stone-voices/vasvas/hardware/vasvas.kicad_sch

## KiCad design hardware/vasvas.kicad_sch (2025-12-18, an earlier design)

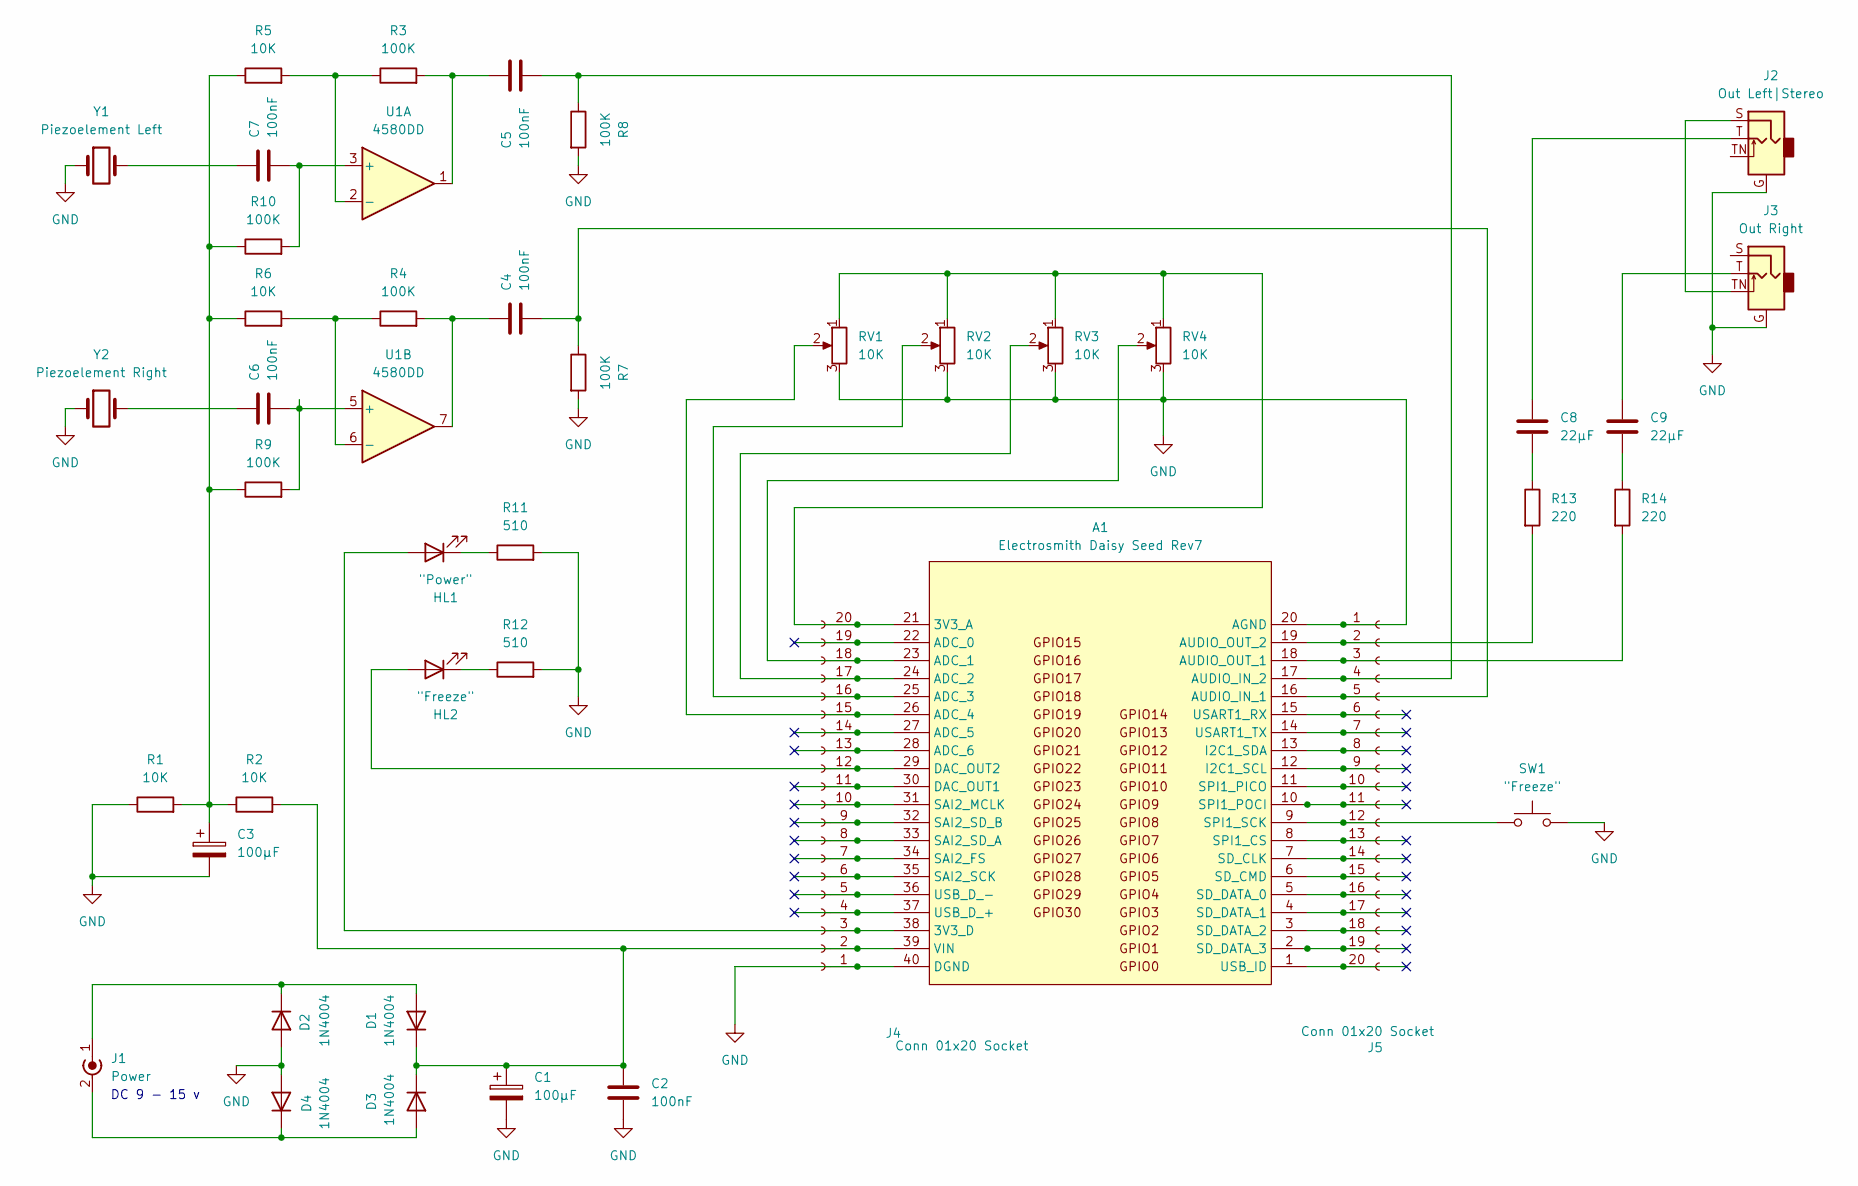
[picture p4: schematic vasvas.kicad_sch]

Parts:
A1: Electrosmith Daisy Seed Rev7
C1, C3: 100µF
C2, C4, C5, C6, C7: 100nF; C_0805_2012Metric
C8, C9: 22µF; C_0805_2012Metric
D1, D2, D3, D4: 1N4004; D_DO-41_SOD81_P10.16mm_Horizontal
HL1: "Power"
HL2: "Freeze"
J1: Power
J2: Out Left|Stereo
J3: Out Right
J4, J5: Conn 01x20 Socket; PinSocket1x20_P2.54mm_Vertical_JLCPCB
R1, R2, R5, R6: 10K; R_0805_2012Metric
R3, R4, R7, R8, R9, R10: 100K; R_0805_2012Metric
R11, R12: 510; R_0805_2012Metric
R13, R14: 220; R_0805_2012Metric
RV1, RV2, RV3, RV4: 10K
SW1: "Freeze"
U1: 4580DD
Y1: Piezoelement Left
Y2: Piezoelement Right

Connections:
GND: A1.20 (AGND), A1.40 (DGND), C1.2, C2.2, C3.2, D2.2 (A), D4.2 (A), J2.G, J3.G, J4.1, J5.1, R1.1, R7.2, R8.2, R11.2, R12.2, RV1.3, RV2.3, RV3.3, RV4.3, SW1.3 (B), SW1.4 (B), Y1.1, Y2.1
unnamed: A1.1 (USB_ID), J5.20
unnamed: A1.2 (SD_DATA_3), J5.19
unnamed: A1.3 (SD_DATA_2), J5.18
unnamed: A1.4 (SD_DATA_1), J5.17
unnamed: A1.5 (SD_DATA_0), J5.16
unnamed: A1.6 (SD_CMD), J5.15
unnamed: A1.7 (SD_CLK), J5.14
unnamed: A1.8 (SPI1_CS), J5.13
unnamed: A1.9 (SPI1_SCK), J5.12, SW1.1 (A), SW1.2 (A)
unnamed: A1.10 (SPI1_POCI), J5.11
unnamed: A1.11 (SPI1_PICO), J5.10
unnamed: A1.12 (I2C1_SCL), J5.9
unnamed: A1.13 (I2C1_SDA), J5.8
unnamed: A1.14 (USART1_TX), J5.7
unnamed: A1.15 (USART1_RX), J5.6
unnamed: A1.16 (AUDIO_IN_1), C4.2, J5.5, R7.1
unnamed: A1.17 (AUDIO_IN_2), C5.2, J5.4, R8.1
unnamed: A1.18 (AUDIO_OUT_1), J5.3, R14.2
unnamed: A1.19 (AUDIO_OUT_2), J5.2, R13.2
unnamed: A1.21 (3V3_A), J4.20, RV1.1, RV2.1, RV3.1, RV4.1
unnamed: A1.22 (ADC_0), J4.19
unnamed: A1.23 (ADC_1), J4.18, RV4.2
unnamed: A1.24 (ADC_2), J4.17, RV3.2
unnamed: A1.25 (ADC_3), J4.16, RV2.2
unnamed: A1.26 (ADC_4), J4.15, RV1.2
unnamed: A1.27 (ADC_5), J4.14
unnamed: A1.28 (ADC_6), J4.13
unnamed: A1.29 (DAC_OUT2), HL2.2 (A), J4.12
unnamed: A1.30 (DAC_OUT1), J4.11
unnamed: A1.31 (SAI2_MCLK), J4.10
unnamed: A1.32 (SAI2_SD_B), J4.9
unnamed: A1.33 (SAI2_SD_A), J4.8
unnamed: A1.34 (SAI2_FS), J4.7
unnamed: A1.35 (SAI2_SCK), J4.6
unnamed: A1.36 (USB_D_-), J4.5
unnamed: A1.37 (USB_D_+), J4.4
unnamed: A1.38 (3V3_D), HL1.2 (A), J4.3
unnamed: A1.39 (VIN), C1.1, C2.1, D1.1 (K), D3.1 (K), J4.2, R2.2
unnamed: C3.1, R1.2, R2.1, R5.1, R6.1, R9.1, R10.1
unnamed: C4.1, R4.2, U1.7
unnamed: C5.1, R3.2, U1.1
unnamed: C6.1, Y2.2
unnamed: C6.2, R9.2, U1.5 (+)
unnamed: C7.1, Y1.2
unnamed: C7.2, R10.2, U1.3 (+)
unnamed: C8.1, J2.T
unnamed: C8.2, R13.1
unnamed: C9.1, J3.T
unnamed: C9.2, R14.1
unnamed: D1.2 (A), D2.1 (K), J1.1 (In)
unnamed: D3.2 (A), D4.1 (K), J1.2 (Ext)
unnamed: HL1.1 (K), R11.1
unnamed: HL2.1 (K), R12.1
unnamed: J2.S, J3.TN
unnamed: R3.1, R5.2, U1.2 (-)
unnamed: R4.1, R6.2, U1.6 (-)

Notes on the sheet:
DC 9 - 15 v
